BenjaminPoilve/MiniChord/documentation/docs/ressources/all_buttons.jpg

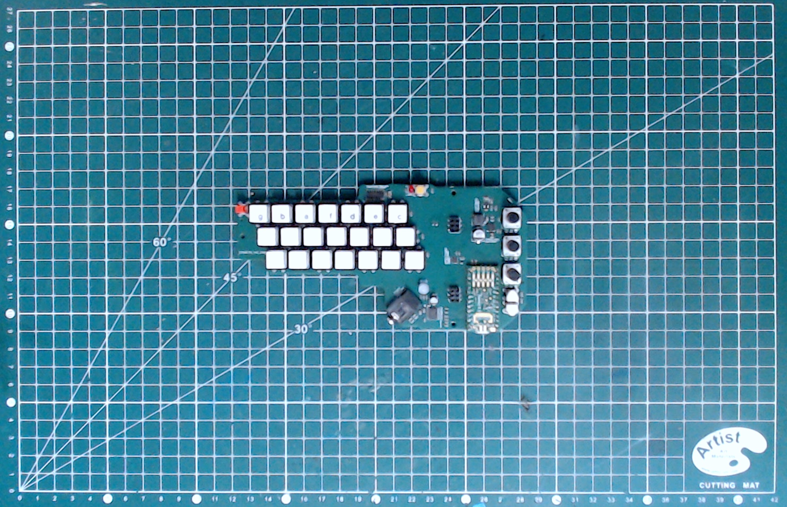
documentation/docs/ressources/all_buttons.jpg
