BenjaminPoilve/MiniChord/documentation/docs/ressources/bg3.jpg

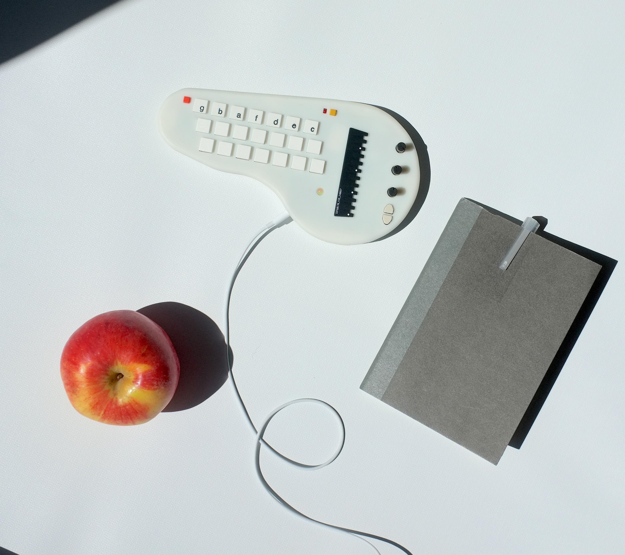
documentation/docs/ressources/bg3.jpg
