BenjaminPoilve/MiniChord/documentation/docs/ressources/big_backup/6060_resin.png

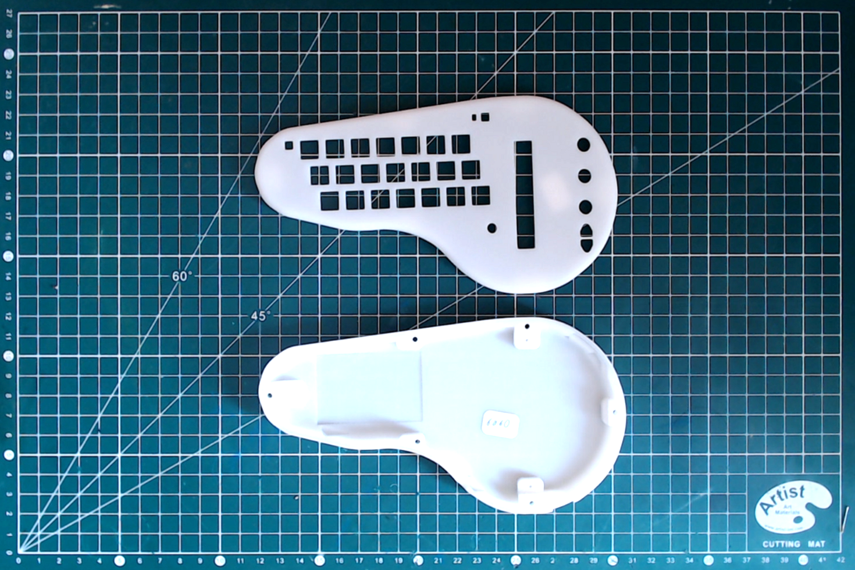
documentation/docs/ressources/big_backup/6060_resin.png
