BenjaminPoilve/MiniChord/documentation/docs/ressources/big_backup/board_ok.png

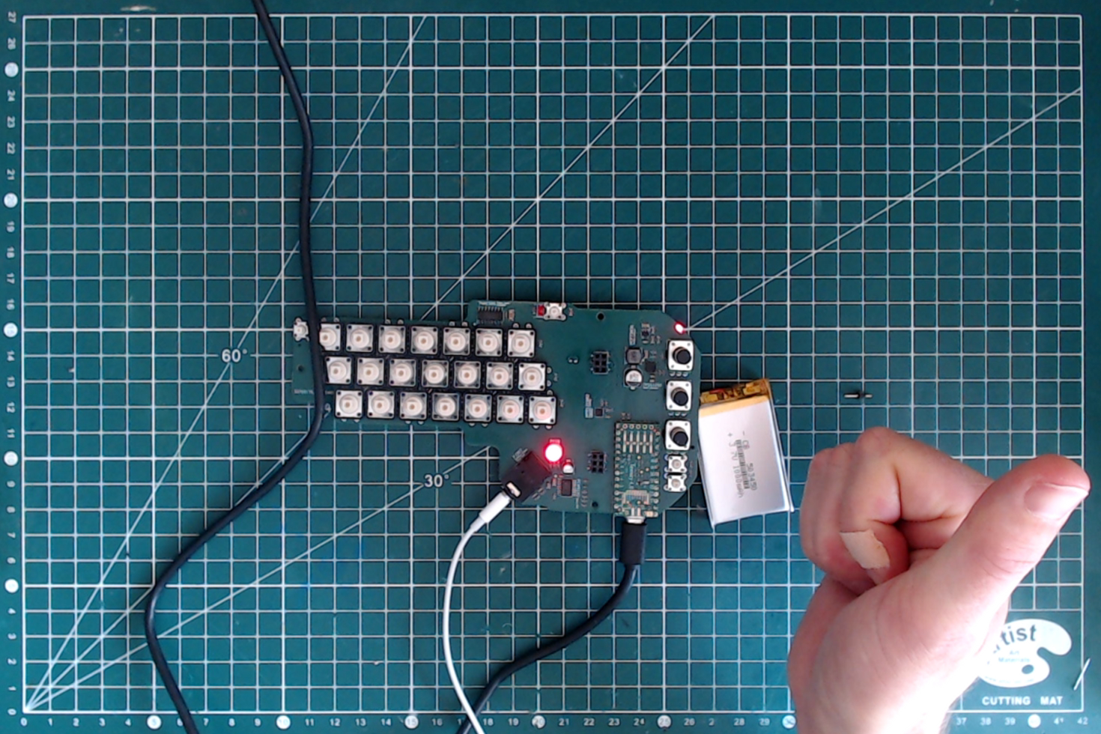
documentation/docs/ressources/big_backup/board_ok.png
