BenjaminPoilve/MiniChord/documentation/docs/ressources/big_backup/both_pcb.jpg

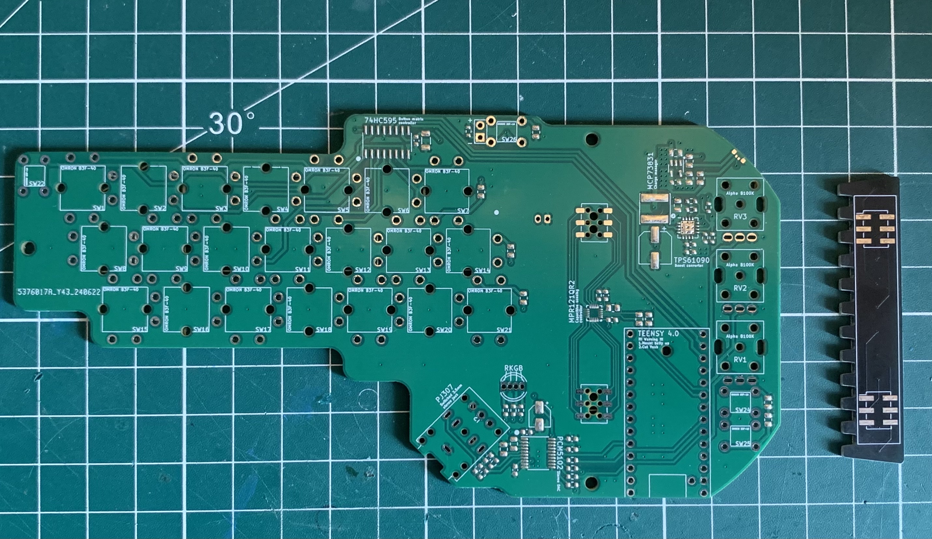
documentation/docs/ressources/big_backup/both_pcb.jpg
