BenjaminPoilve/MiniChord/documentation/docs/ressources/big_backup/button_cutting.png

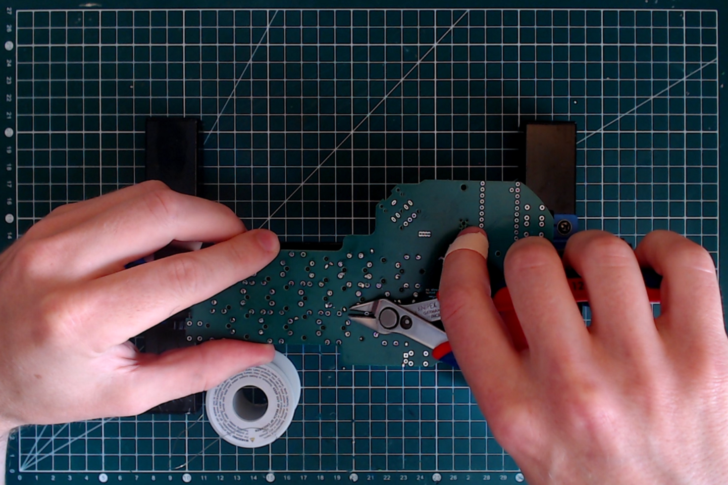
documentation/docs/ressources/big_backup/button_cutting.png
