BenjaminPoilve/MiniChord/documentation/docs/ressources/big_backup/button_insertion.png

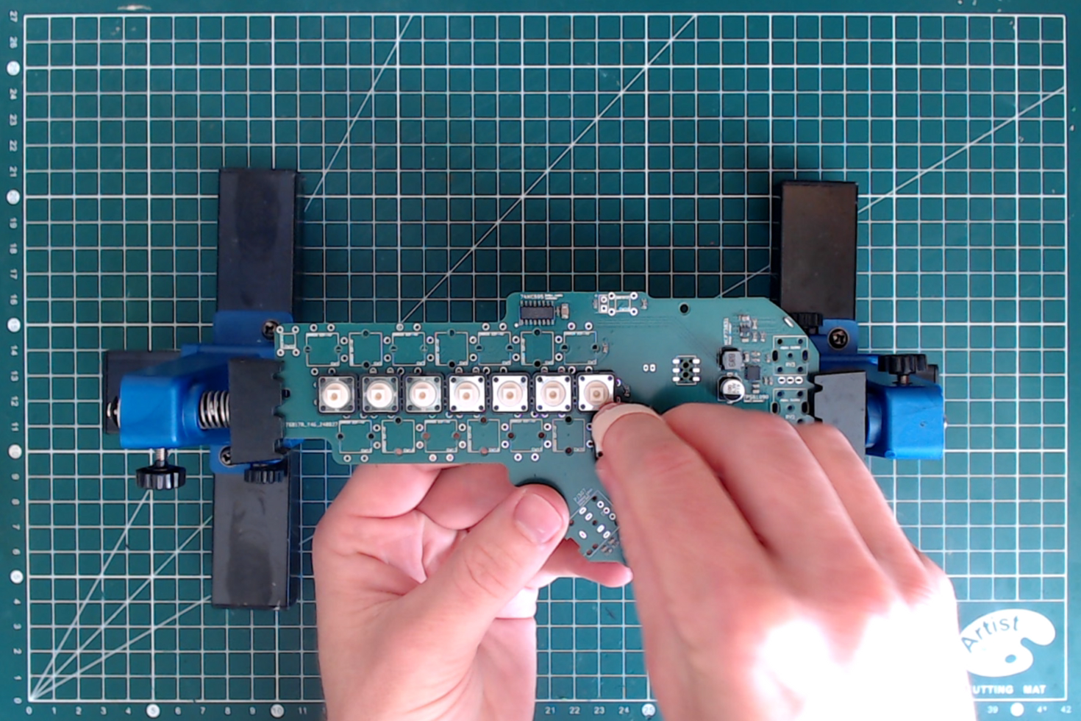
documentation/docs/ressources/big_backup/button_insertion.png
