BenjaminPoilve/MiniChord/documentation/docs/ressources/big_backup/connector_batt.png

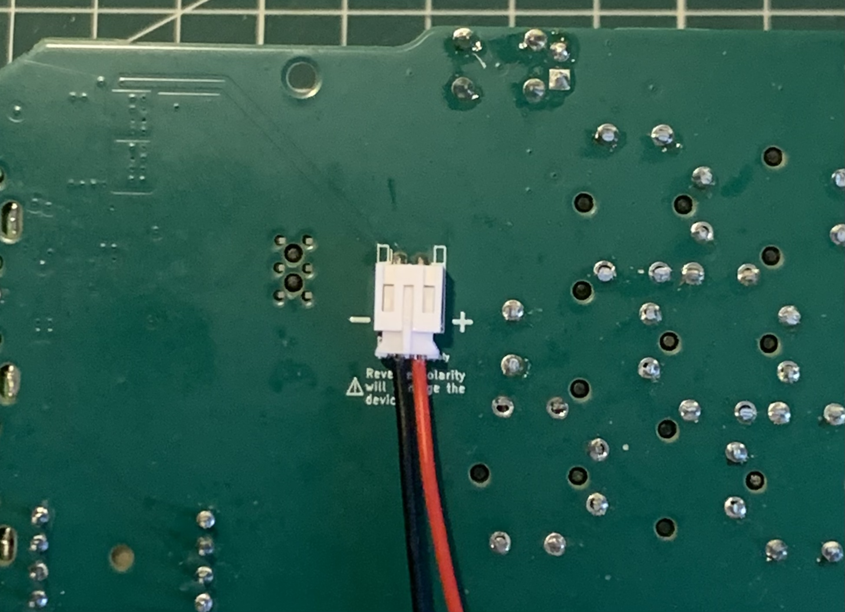
documentation/docs/ressources/big_backup/connector_batt.png
