BenjaminPoilve/MiniChord/documentation/docs/ressources/big_backup/dyed_shell.png

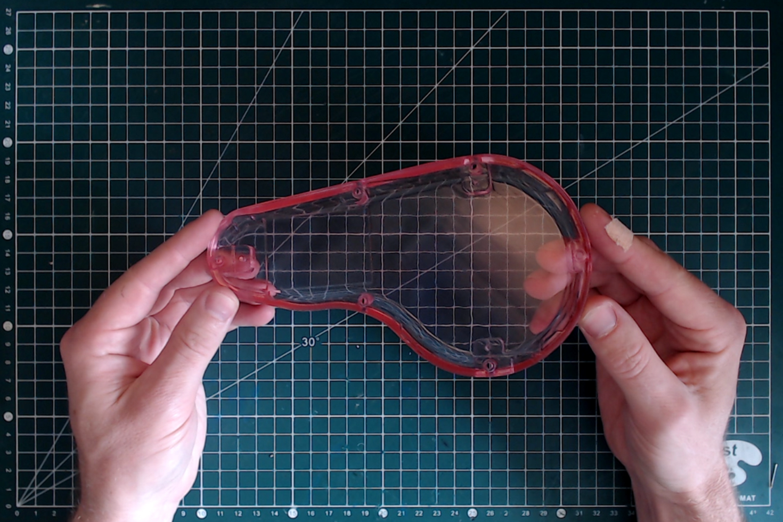
documentation/docs/ressources/big_backup/dyed_shell.png
