BenjaminPoilve/MiniChord/documentation/docs/ressources/big_backup/fdm_shells.png

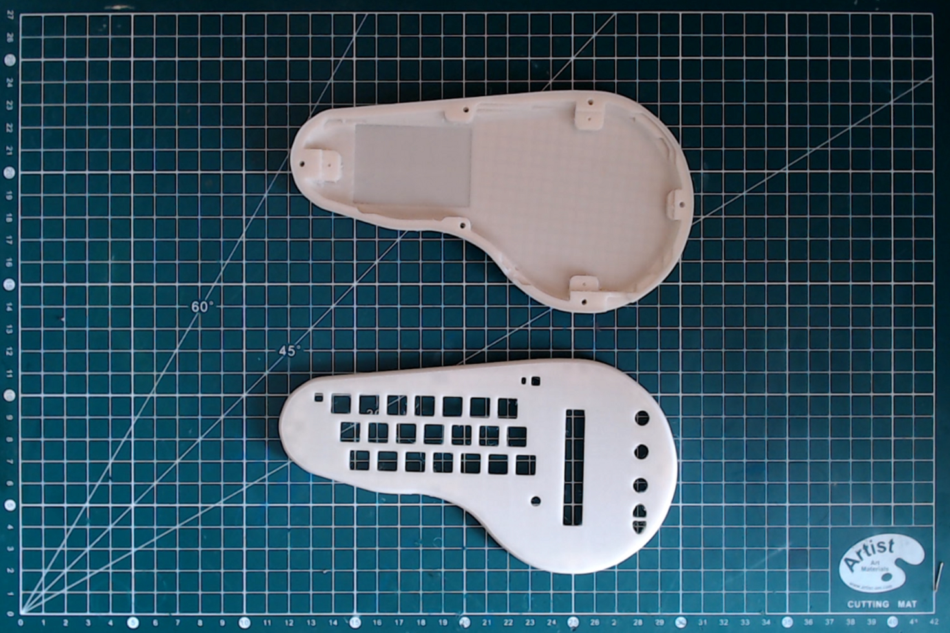
documentation/docs/ressources/big_backup/fdm_shells.png
