BenjaminPoilve/MiniChord/documentation/docs/ressources/big_backup/header.png

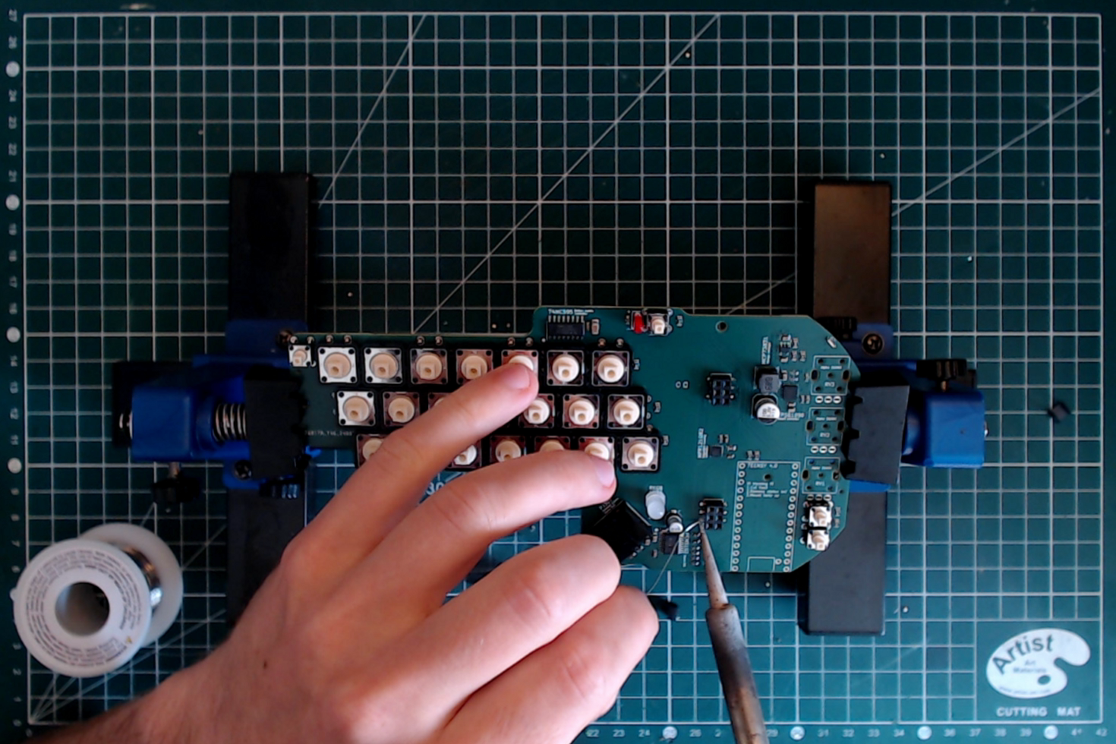
documentation/docs/ressources/big_backup/header.png
