BenjaminPoilve/MiniChord/documentation/docs/ressources/big_backup/led_red.png

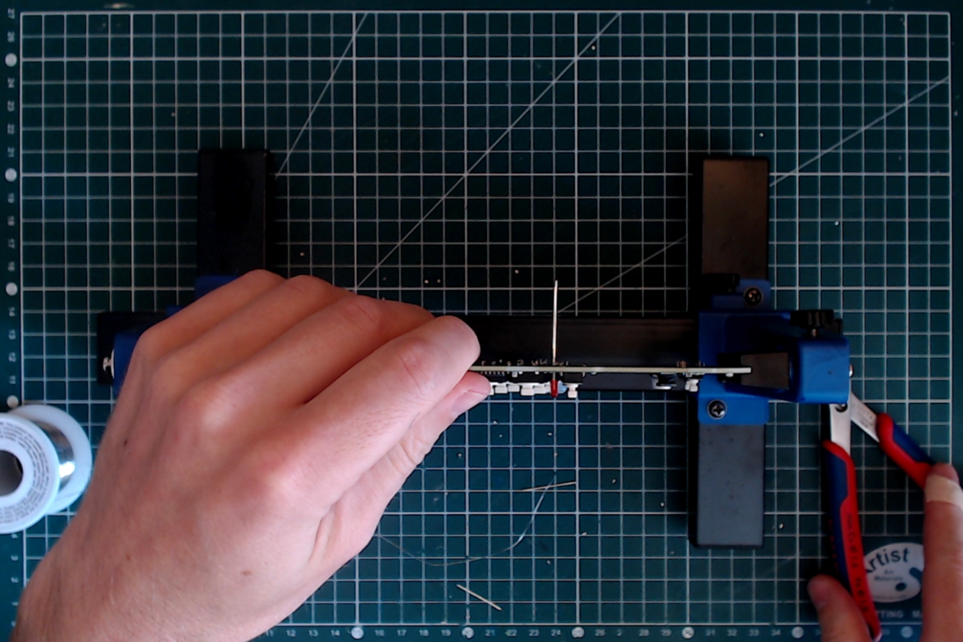
documentation/docs/ressources/big_backup/led_red.png
