BenjaminPoilve/MiniChord/documentation/docs/ressources/big_backup/led_rgb.png

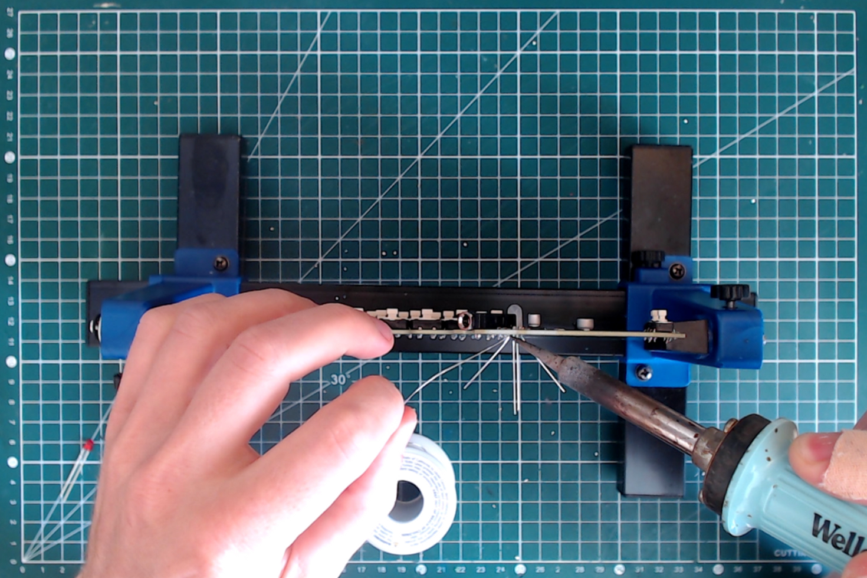
documentation/docs/ressources/big_backup/led_rgb.png
