BenjaminPoilve/MiniChord/documentation/docs/ressources/big_backup/ok_led.png

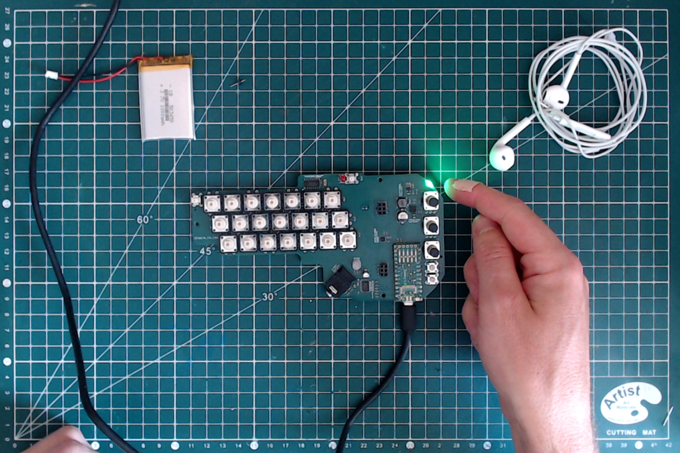
documentation/docs/ressources/big_backup/ok_led.png
