BenjaminPoilve/MiniChord/documentation/docs/ressources/big_backup/ok_led_red.png

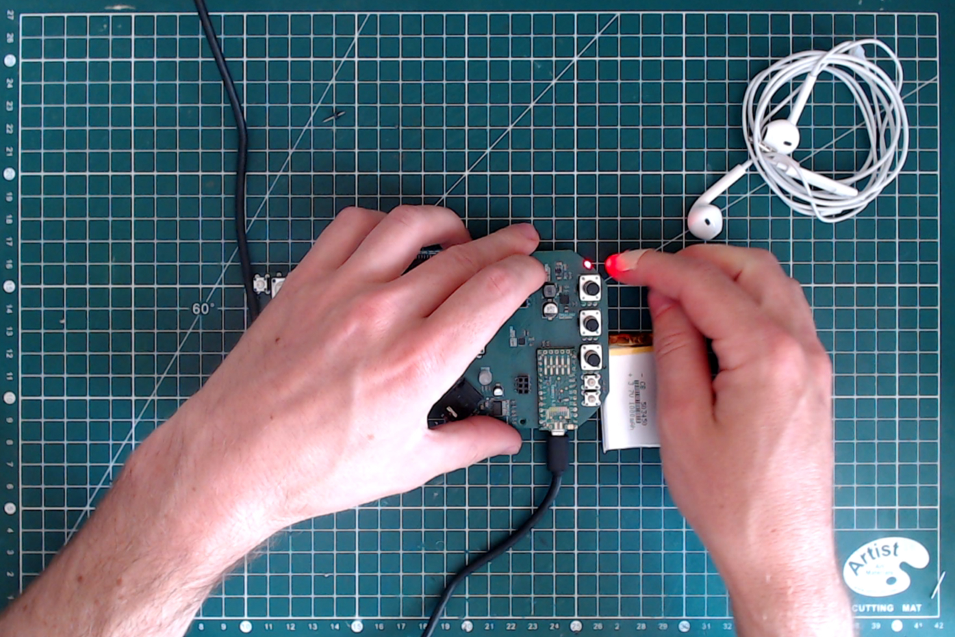
documentation/docs/ressources/big_backup/ok_led_red.png
