BenjaminPoilve/MiniChord/documentation/docs/ressources/big_backup/pot_cut.png

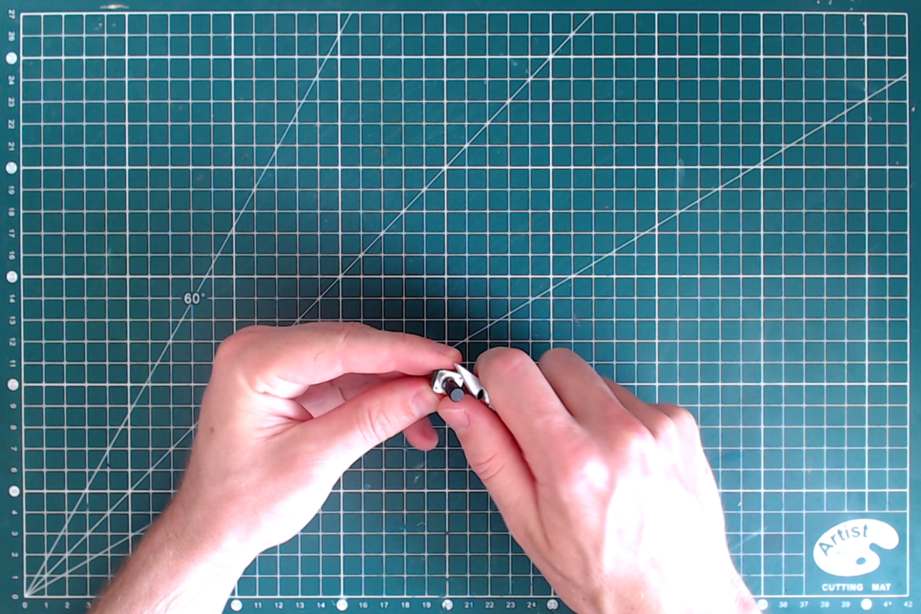
documentation/docs/ressources/big_backup/pot_cut.png
