BenjaminPoilve/MiniChord/documentation/docs/ressources/big_backup/potentiometer_seat.png

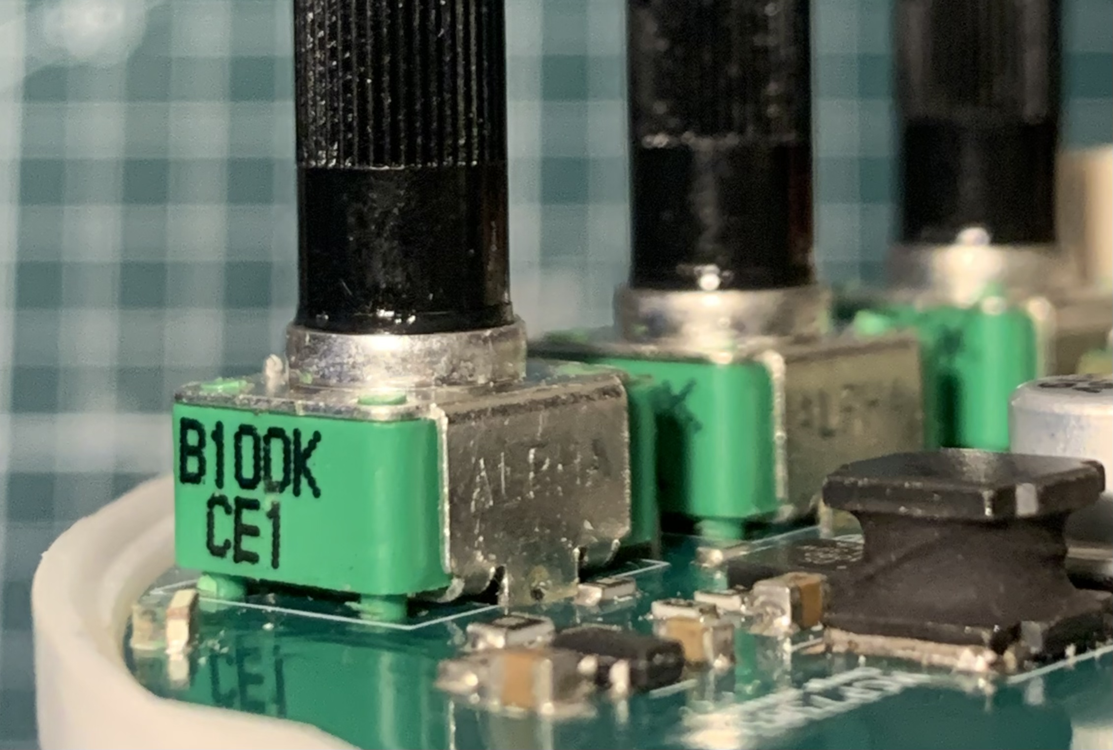
documentation/docs/ressources/big_backup/potentiometer_seat.png
