BenjaminPoilve/MiniChord/documentation/docs/ressources/big_backup/smd.jpg

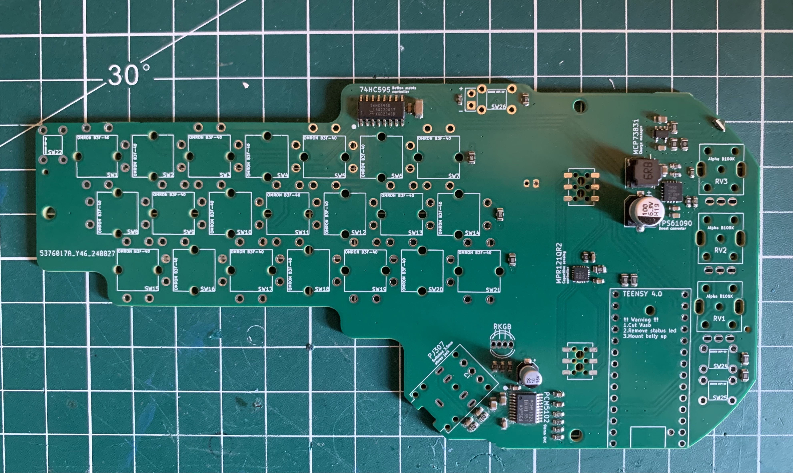
documentation/docs/ressources/big_backup/smd.jpg
