BenjaminPoilve/MiniChord/documentation/docs/ressources/big_backup/teensy_cut.png

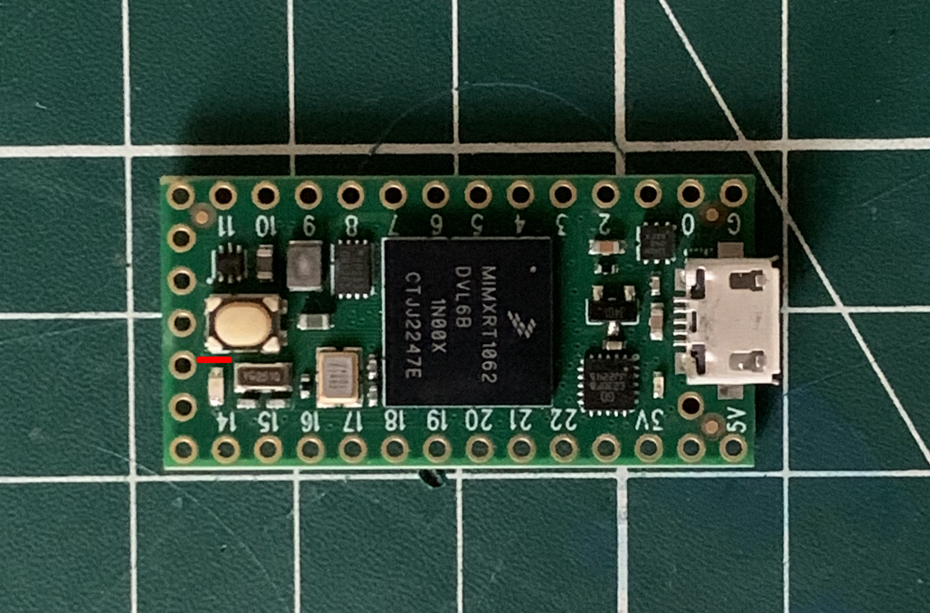
documentation/docs/ressources/big_backup/teensy_cut.png
