BenjaminPoilve/MiniChord/documentation/docs/ressources/big_backup/teensy_cutting.png

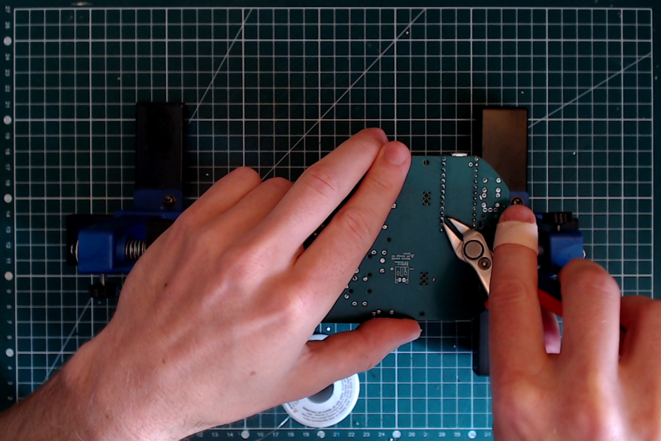
documentation/docs/ressources/big_backup/teensy_cutting.png
