BenjaminPoilve/MiniChord/documentation/docs/ressources/big_backup/teensy_led.png

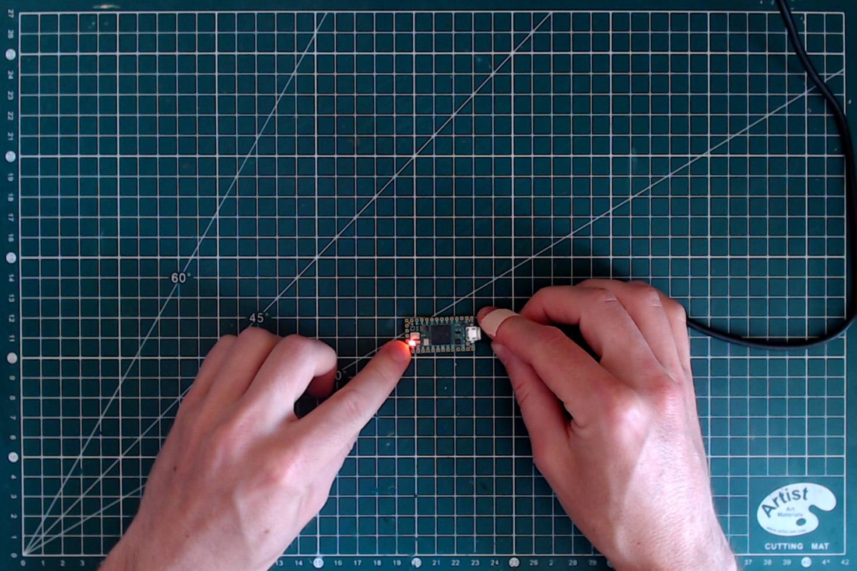
documentation/docs/ressources/big_backup/teensy_led.png
