BenjaminPoilve/MiniChord/documentation/docs/ressources/big_backup/teensy_power_check.png

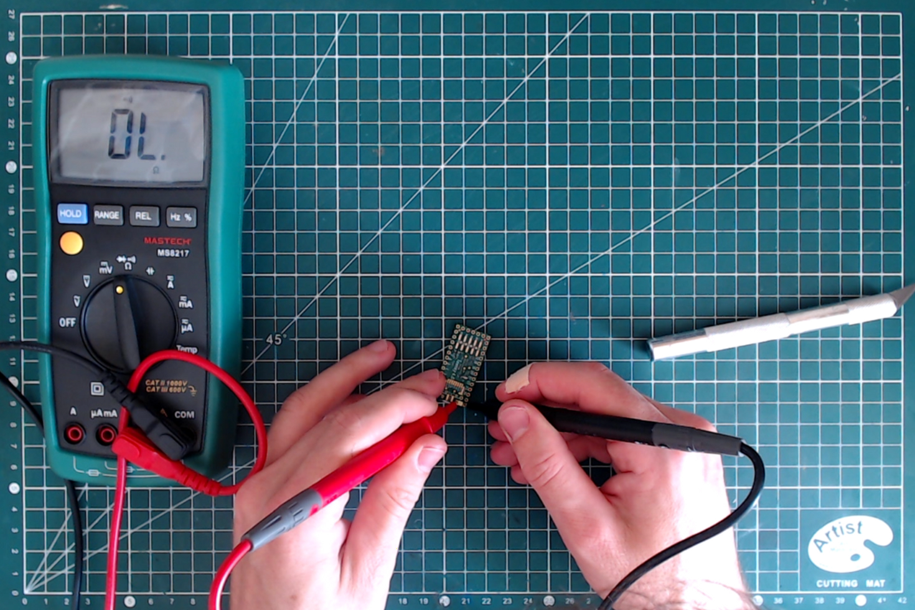
documentation/docs/ressources/big_backup/teensy_power_check.png
