BenjaminPoilve/MiniChord/documentation/docs/ressources/big_backup/teensy_power_cut.png

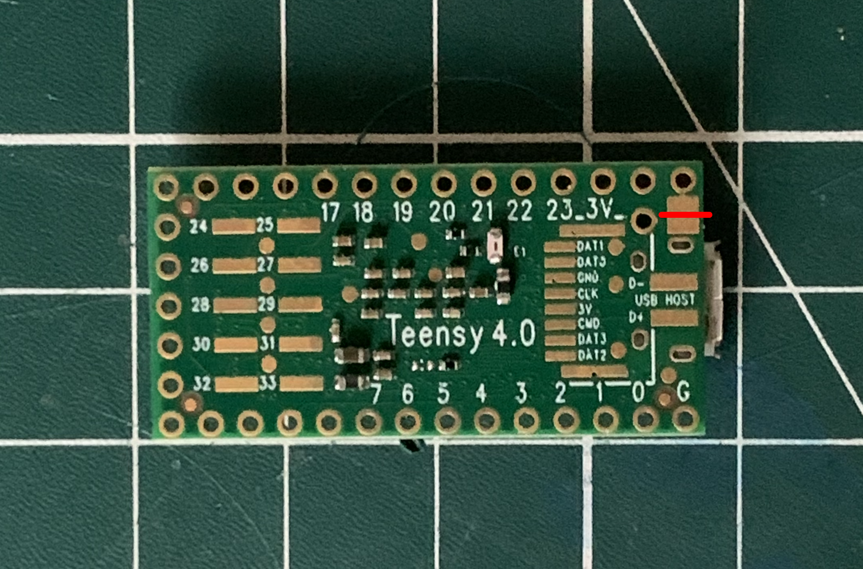
documentation/docs/ressources/big_backup/teensy_power_cut.png
