BenjaminPoilve/MiniChord/documentation/docs/ressources/big_backup/teensy_tacking.png

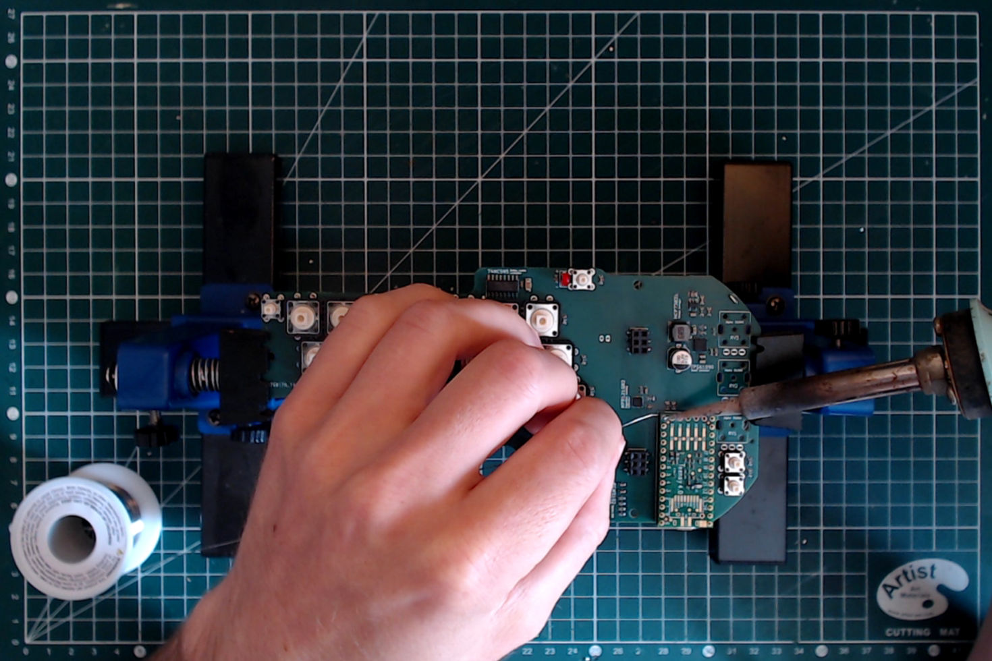
documentation/docs/ressources/big_backup/teensy_tacking.png
