BenjaminPoilve/MiniChord/documentation/docs/ressources/big_backup/transparent.png

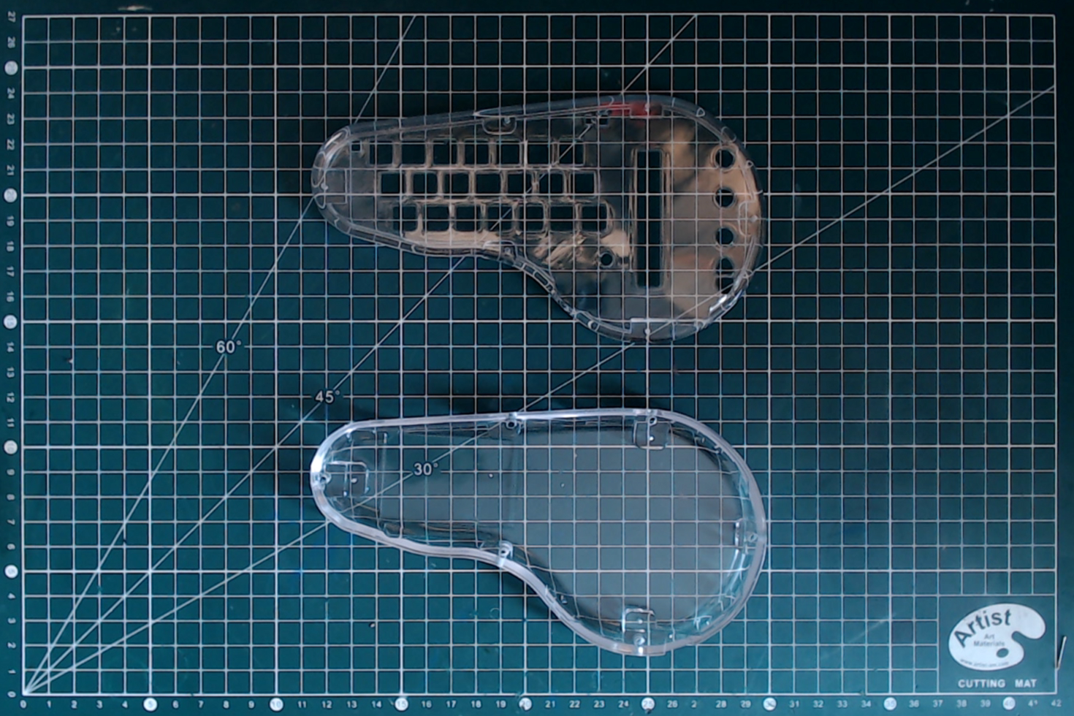
documentation/docs/ressources/big_backup/transparent.png
