BenjaminPoilve/MiniChord/documentation/docs/ressources/button_cutting.jpg

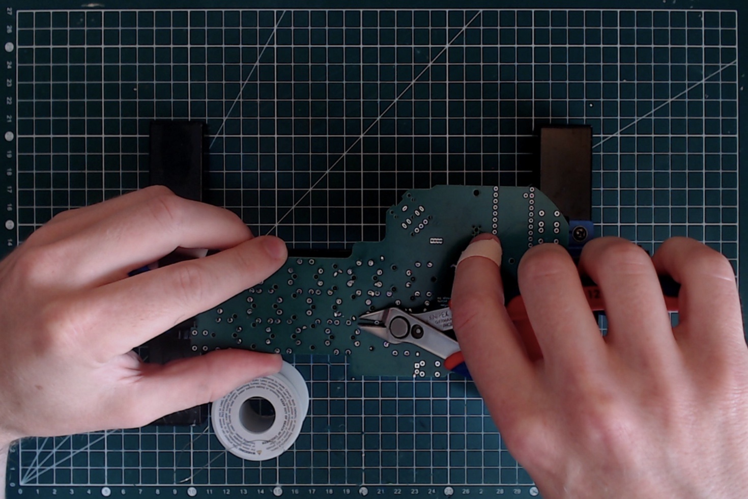
documentation/docs/ressources/button_cutting.jpg
