BenjaminPoilve/MiniChord/documentation/docs/ressources/drawing_10.png.png

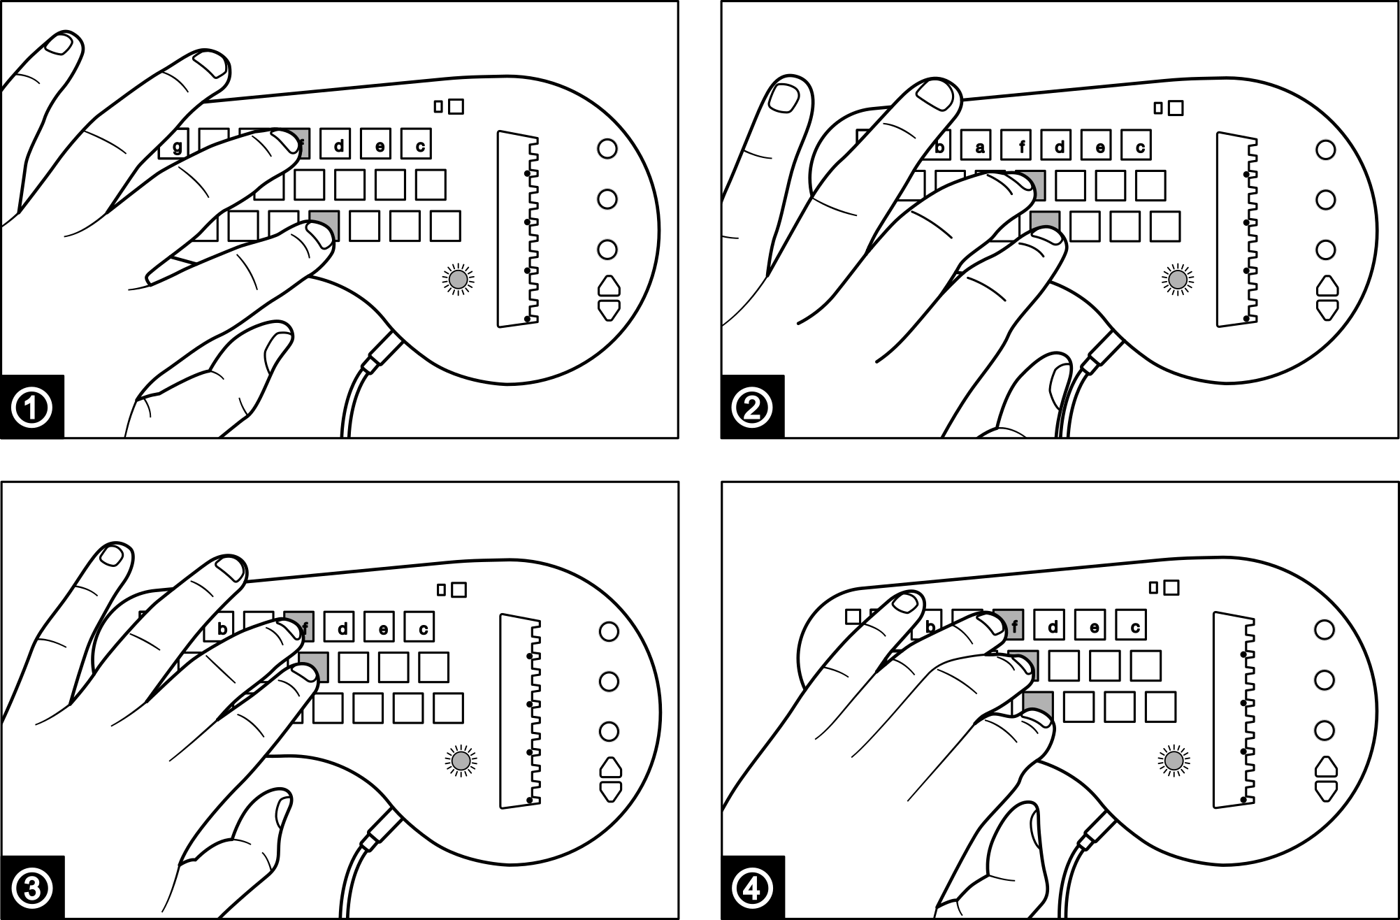
documentation/docs/ressources/drawing_10.png.png
