BenjaminPoilve/MiniChord/documentation/docs/ressources/pot_cutted.jpg

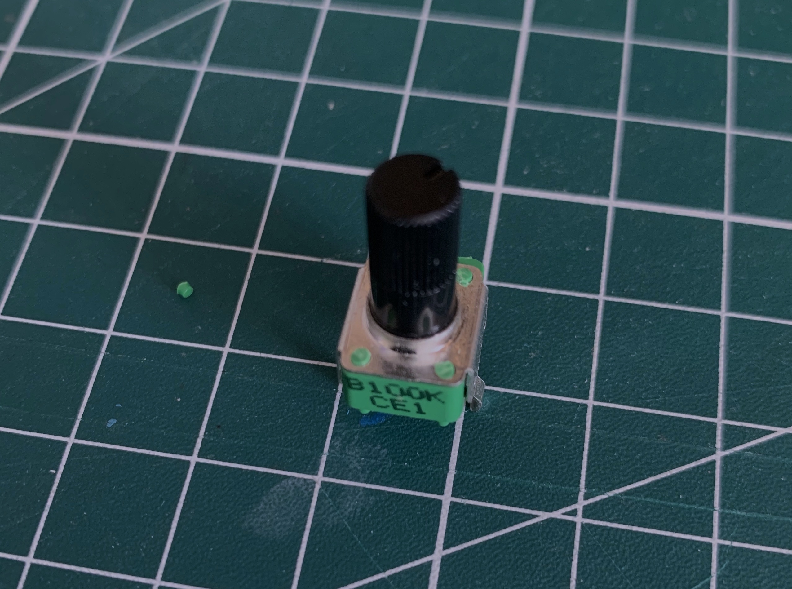
documentation/docs/ressources/pot_cutted.jpg
