BenjaminPoilve/MiniChord/documentation/docs/ressources/pouch_attached.jpg

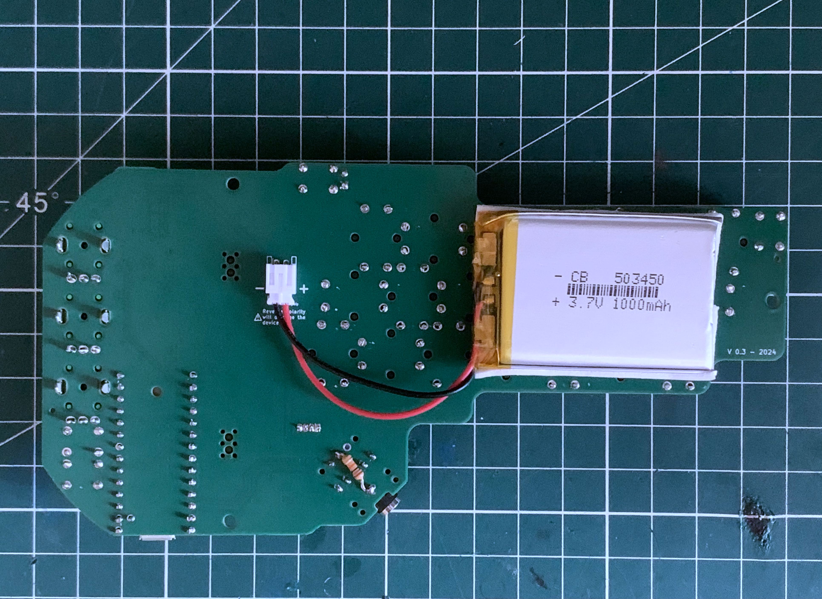
documentation/docs/ressources/pouch_attached.jpg
