BenjaminPoilve/MiniChord/documentation/docs/ressources/scotched_battery.jpg

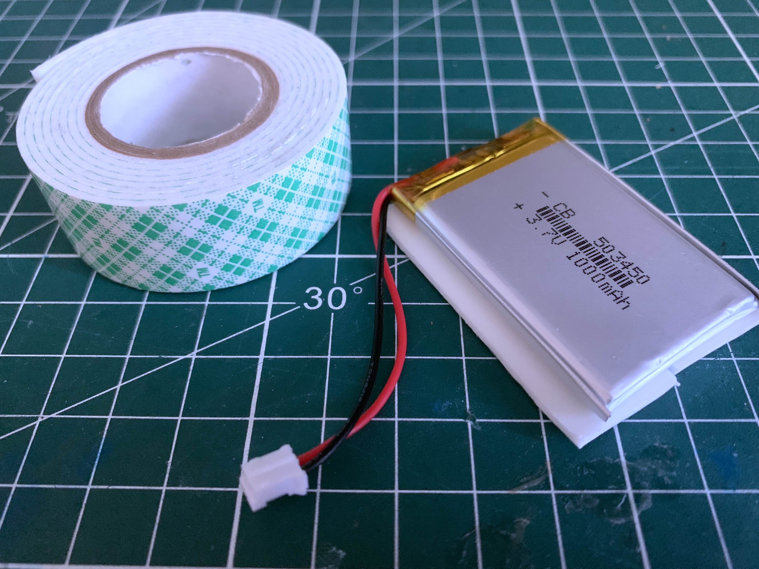
documentation/docs/ressources/scotched_battery.jpg
