BenjaminPoilve/MiniChord/hardware/3D/DXF/MiniChord-User_pcb_support.dxf

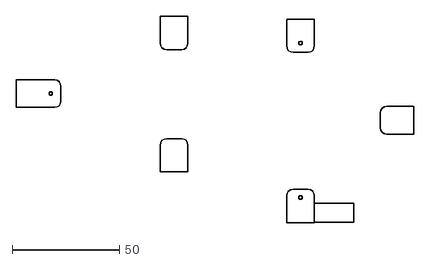
[picture p46: CAD file, 2024-08-28]
hardware/3D/DXF/MiniChord-User_pcb_support.dxf
185.2 x 96.2
