BenjaminPoilve/MiniChord/hardware/3D/DXF/buttons.dxf

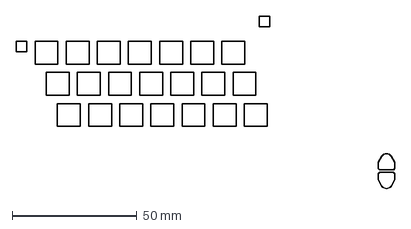
[picture p47: CAD file, 2024-08-28]
hardware/3D/DXF/buttons.dxf
151.8 x 69.1 mm
