BenjaminPoilve/MiniChord/hardware/3D/DXF/potentiometers.dxf

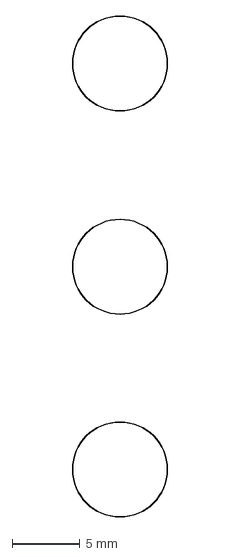
[picture p48: CAD file, 2024-08-28]
hardware/3D/DXF/potentiometers.dxf
7.00 x 37.0 mm
