BenjaminPoilve/MiniChord/hardware/3D/DXF/MiniChord-User_Eco2.dxf

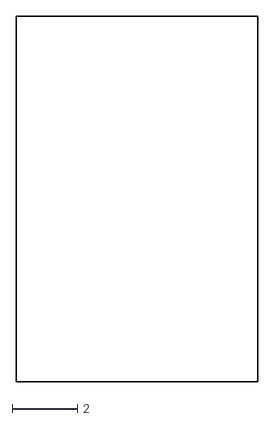
[picture p49: CAD file, 2024-08-28]
hardware/3D/DXF/MiniChord-User_Eco2.dxf
7.40 x 11.2
