BenjaminPoilve/MiniChord/hardware/3D/DXF/MiniChord-User_holes_housing.dxf

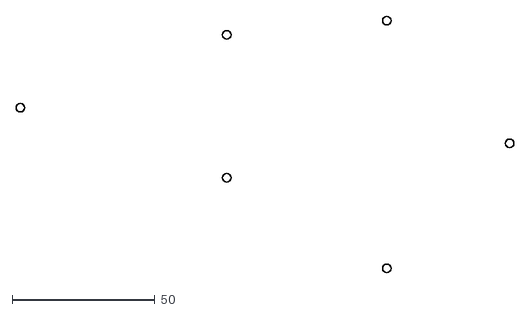
[picture p50: CAD file, 2024-08-28]
hardware/3D/DXF/MiniChord-User_holes_housing.dxf
174.2 x 89.8
