BenjaminPoilve/MiniChord/hardware/3D/DXF/MiniChord-Edge_Cuts.dxf

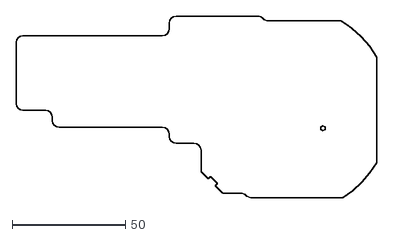
[picture p51: CAD file, 2024-08-28]
hardware/3D/DXF/MiniChord-Edge_Cuts.dxf
159.0 x 80.0
