BenjaminPoilve/MiniChord/hardware/3D/DXF/MiniChord-B_Fab.dxf

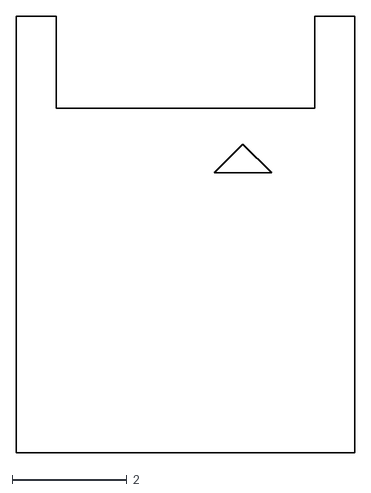
[picture p52: CAD file, 2024-08-28]
hardware/3D/DXF/MiniChord-B_Fab.dxf
5.90 x 7.60
