BenjaminPoilve/MiniChord/hardware/3D/DXF/touch_zone-Edge_Cuts.dxf

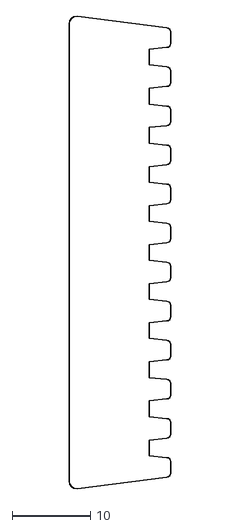
[picture p53: CAD file, 2024-08-28]
hardware/3D/DXF/touch_zone-Edge_Cuts.dxf
13.0 x 60.5
