BenjaminPoilve/MiniChord/hardware/3D/DXF/MiniChord-User_top_edge_curve.dxf

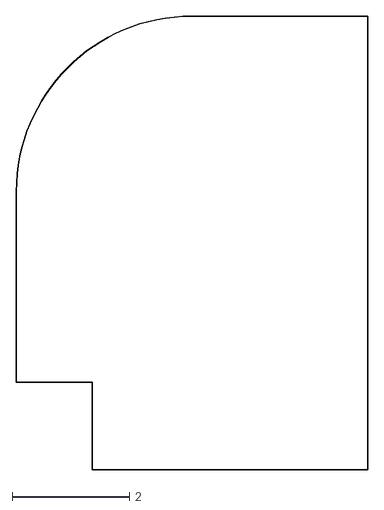
[picture p54: CAD file, 2024-08-28]
hardware/3D/DXF/MiniChord-User_top_edge_curve.dxf
6.00 x 7.75
