BenjaminPoilve/MiniChord/hardware/3D/DXF/MiniChord-User_front_plate_cutout.dxf

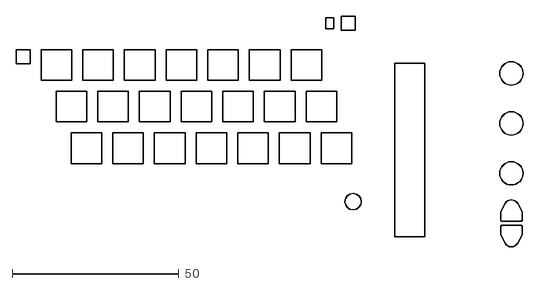
[picture p55: CAD file, 2024-08-28]
hardware/3D/DXF/MiniChord-User_front_plate_cutout.dxf
152.1 x 69.1
