BenjaminPoilve/MiniChord/hardware/3D/DXF/MiniChord-User_front_plate_engraving.dxf

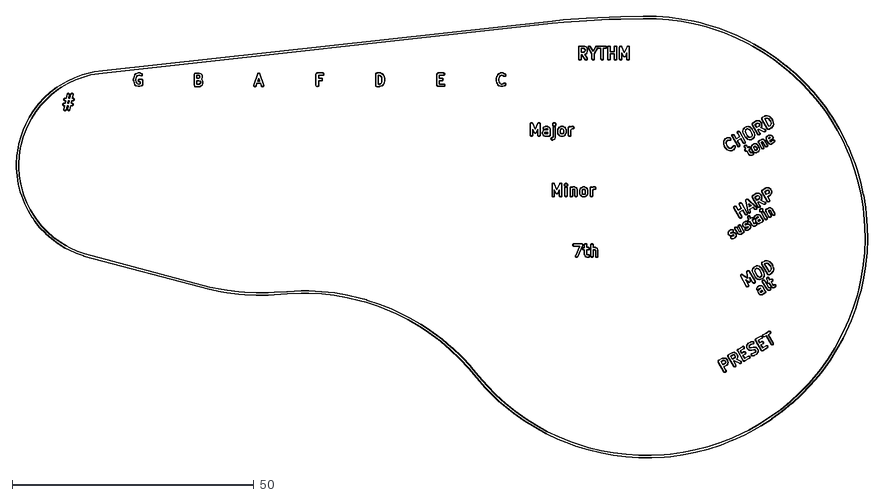
[picture p56: CAD file, 2024-08-28]
hardware/3D/DXF/MiniChord-User_front_plate_engraving.dxf
175.9 x 91.2
