BenjaminPoilve/MiniChord/hardware/3D/DXF/MiniChord-F_Courtyard.dxf

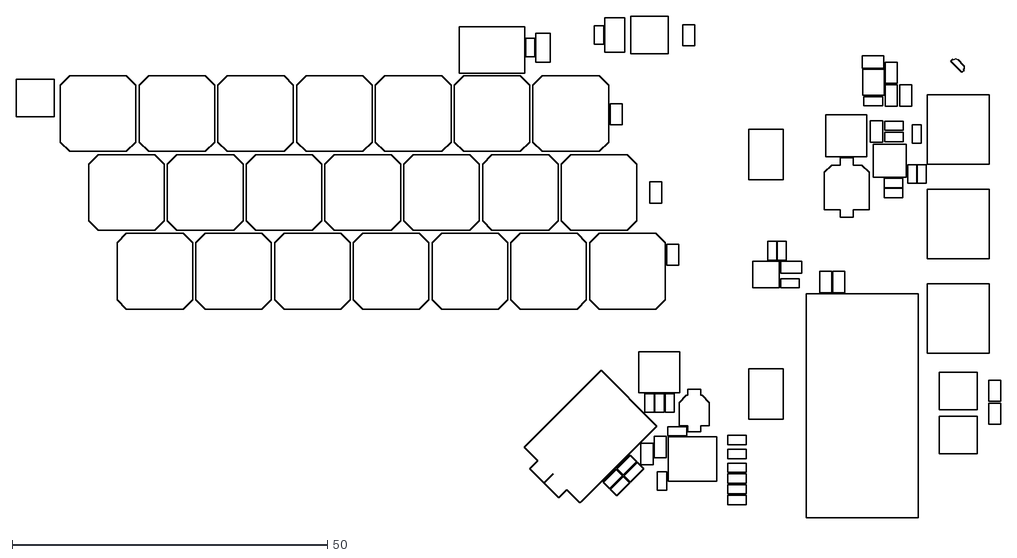
[picture p57: CAD file, 2024-08-28]
hardware/3D/DXF/MiniChord-F_Courtyard.dxf
156.2 x 79.7
