BenjaminPoilve/MiniChord/hardware/3D/DXF/MiniChord-User_top_component_clearance.dxf

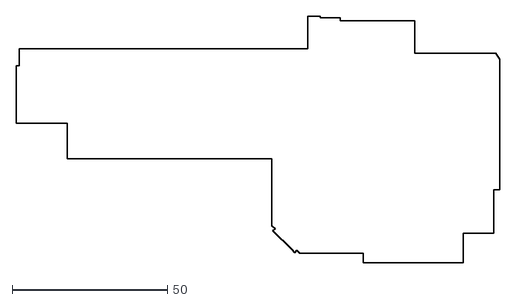
[picture p58: CAD file, 2024-08-28]
hardware/3D/DXF/MiniChord-User_top_component_clearance.dxf
156.0 x 79.5
