BenjaminPoilve/MiniChord/documentation/docs/ressources/big_backup/teensy_soldering.png

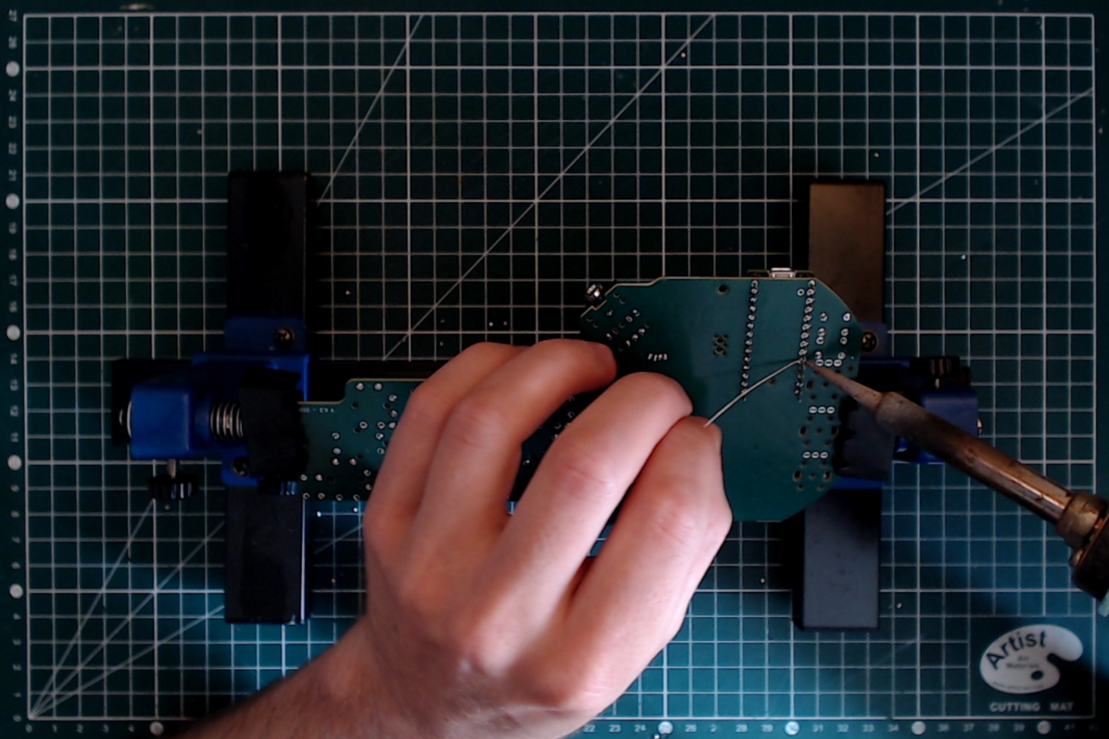
documentation/docs/ressources/big_backup/teensy_soldering.png
