BenjaminPoilve/MiniChord/documentation/site/ressources/smd_assembly/g58221.png

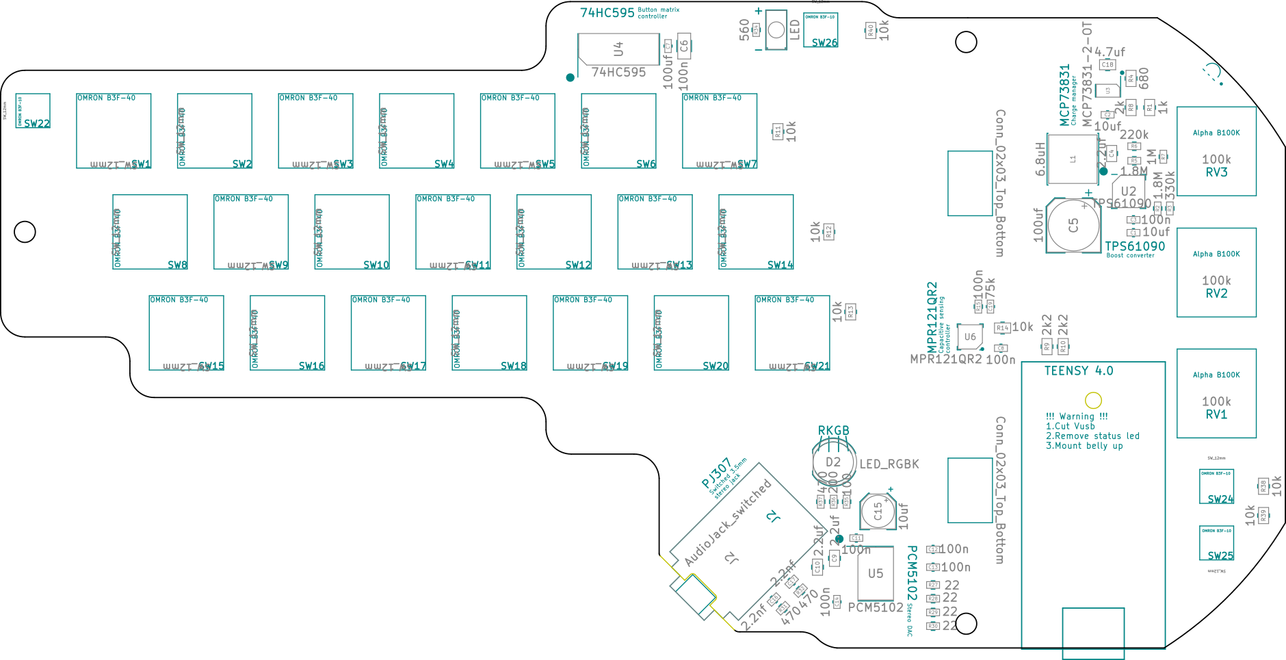
documentation/site/ressources/smd_assembly/g58221.png
